garcianeilangelo-crypto/Dual-logger-PCB-design/echolight_1/allegropcb/CAPC17595_95N_KEM.step

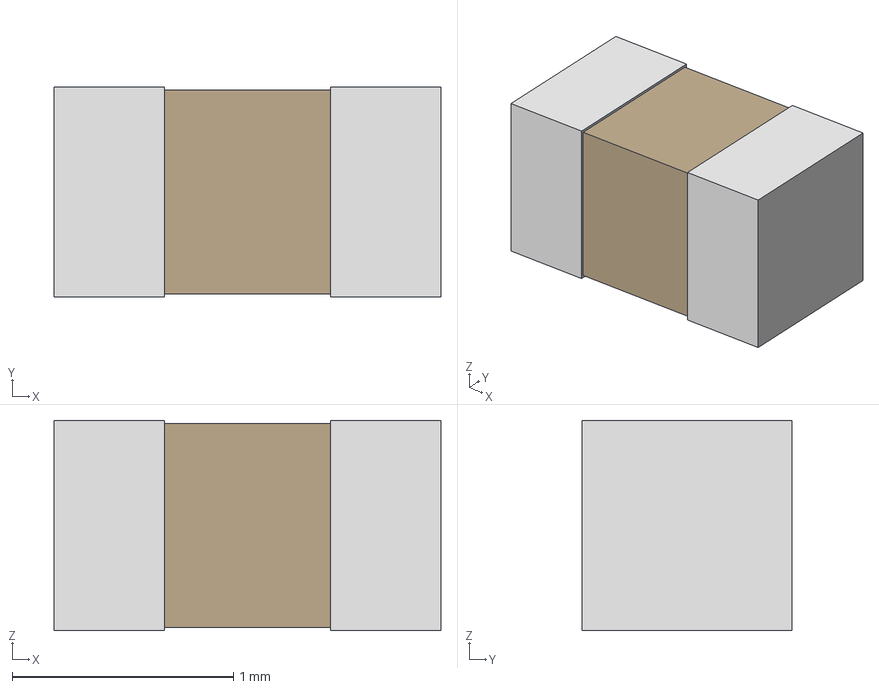
[picture p42: CAD file, 2026-06-25]
echolight_1/allegropcb/CAPC17595_95N_KEM.step
1.75 x 0.95 x 0.95 mm
