garcianeilangelo-crypto/Dual-logger-PCB-design/echolight_1/allegropcb/INDC1608X95N.step

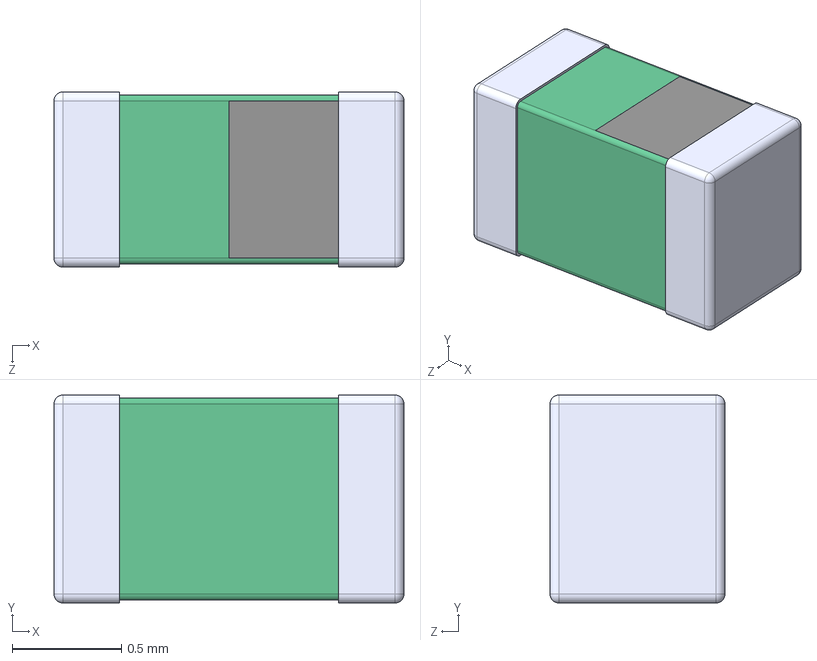
[picture p43: CAD file, 2026-06-25]
echolight_1/allegropcb/INDC1608X95N.step
1.60 x 0.95 x 0.8 mm
