garcianeilangelo-crypto/Dual-logger-PCB-design/echolight_1/allegropcb/IND_1608_TDK.step

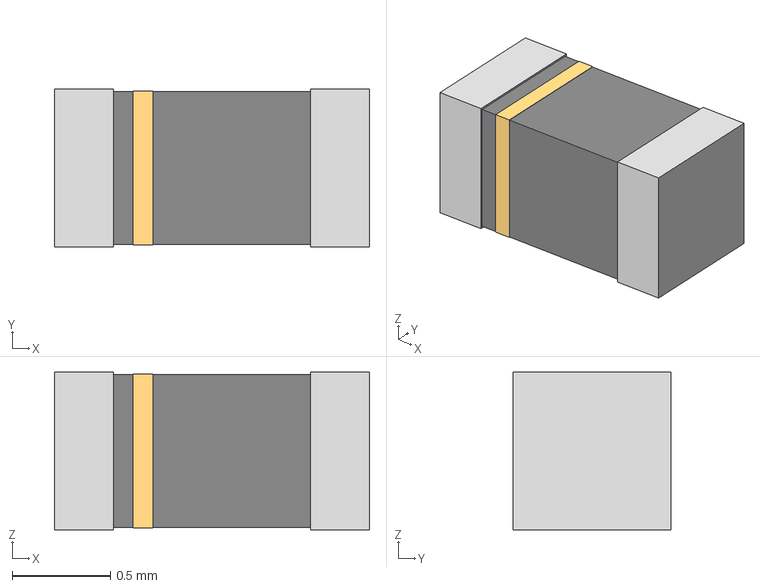
[picture p44: CAD file, 2026-06-25]
echolight_1/allegropcb/IND_1608_TDK.step
1.60 x 0.8 x 0.8 mm
