garcianeilangelo-crypto/Dual-logger-PCB-design/echolight_1/allegropcb/ECWFG70105J.STEP

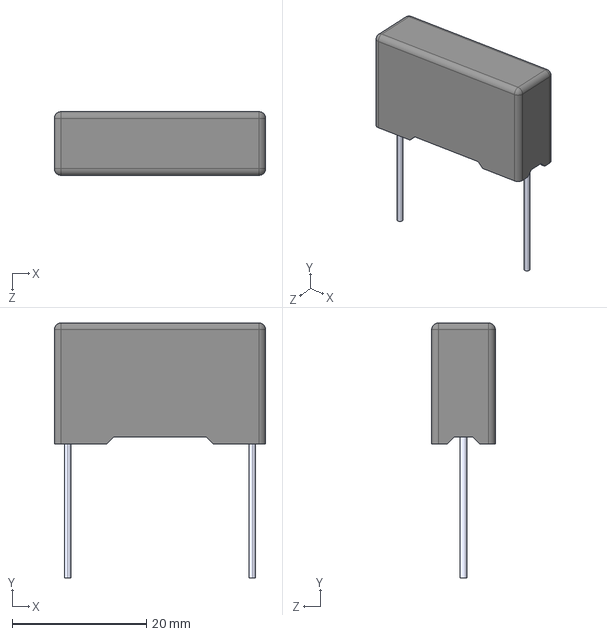
[picture p45: CAD file, 2026-06-25]
echolight_1/allegropcb/ECWFG70105J.STEP
31.5 x 38.0 x 9.50 mm
