garcianeilangelo-crypto/Dual-logger-PCB-design/echolight_1/allegropcb/EEEFN2A100P.step

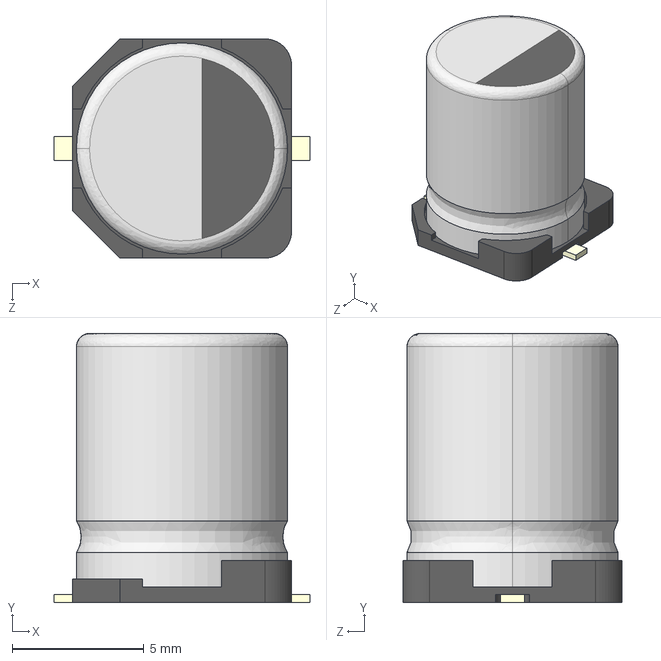
[picture p46: CAD file, 2026-06-25]
echolight_1/allegropcb/EEEFN2A100P.step
9.70 x 10.2 x 8.30 mm
