garcianeilangelo-crypto/Dual-logger-PCB-design/echolight_1/allegropcb/IND_BLM18_0603_MUR.step

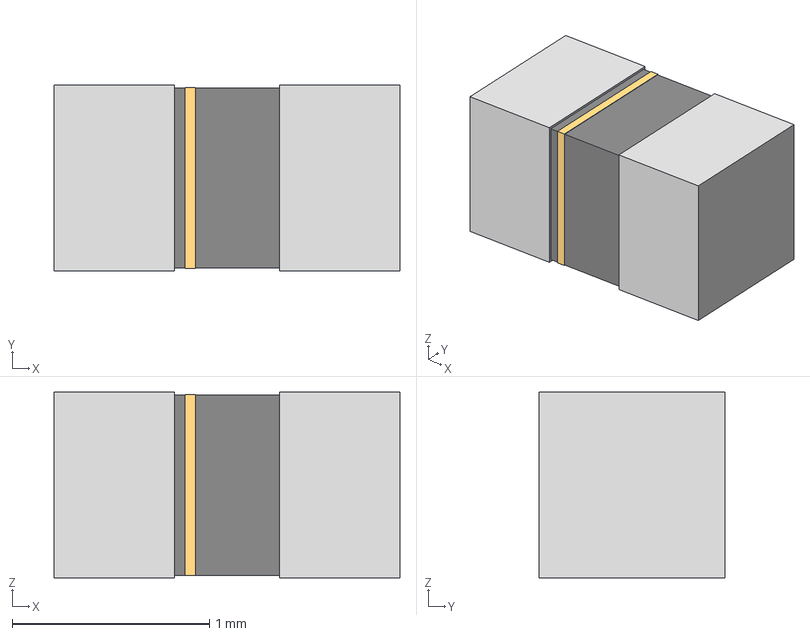
[picture p47: CAD file, 2026-06-25]
echolight_1/allegropcb/IND_BLM18_0603_MUR.step
1.75 x 0.94 x 0.94 mm
