garcianeilangelo-crypto/Dual-logger-PCB-design/echolight_1/allegropcb/CAPC1608X90N.step

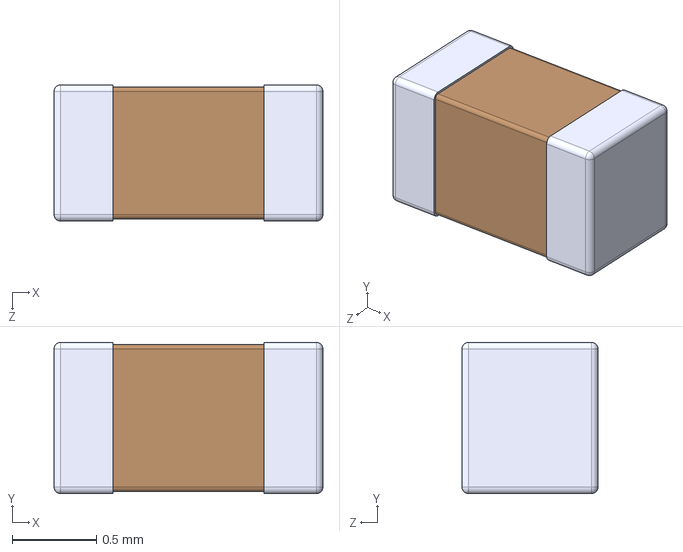
[picture p48: CAD file, 2026-06-25]
echolight_1/allegropcb/CAPC1608X90N.step
1.60 x 0.9 x 0.81 mm
