garcianeilangelo-crypto/Dual-logger-PCB-design/echolight_1/allegropcb/21-0113C_MXM.step

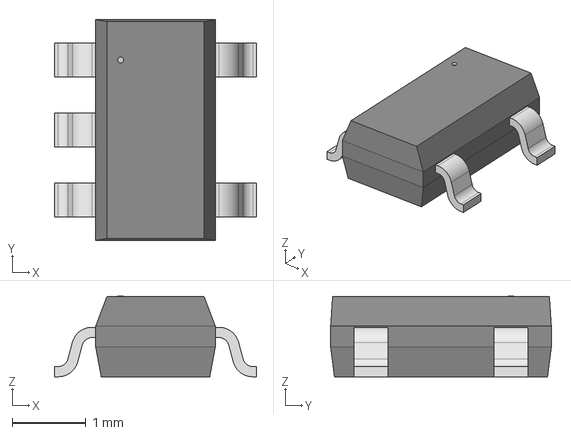
[picture p49: CAD file, 2026-06-25]
echolight_1/allegropcb/21-0113C_MXM.step
2.74 x 3.00 x 1.09 mm
