garcianeilangelo-crypto/Dual-logger-PCB-design/echolight_1/allegropcb/RFANT3216120A5T.stp

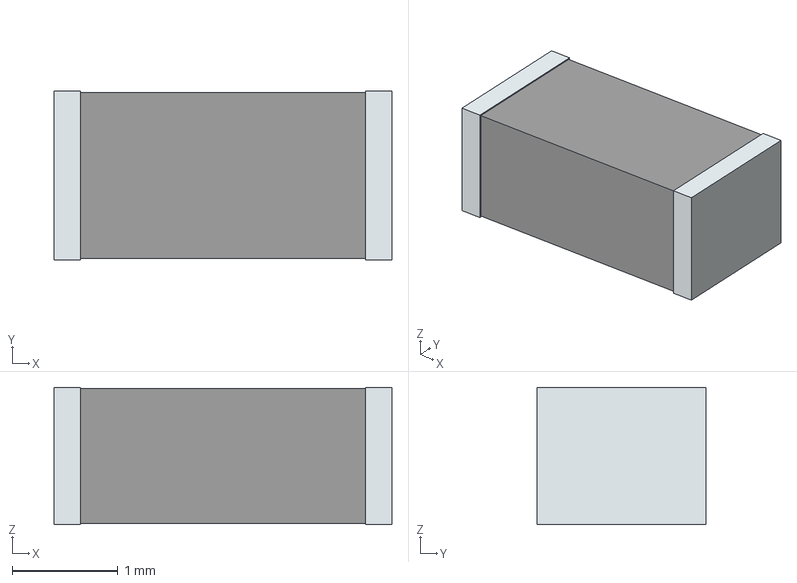
[picture p50: CAD file, 2026-03-18]
echolight_1/allegropcb/RFANT3216120A5T.stp
3.20 x 1.60 x 1.30 mm
term1
term2
